yuntsebaryon/SLArchettoHeaterControl/Schematic/GasHeaterControl/GasHeaterControl.kicad_sch

## KiCad design Schematic/GasHeaterControl/GasHeaterControl.kicad_sch (2023-05-16)

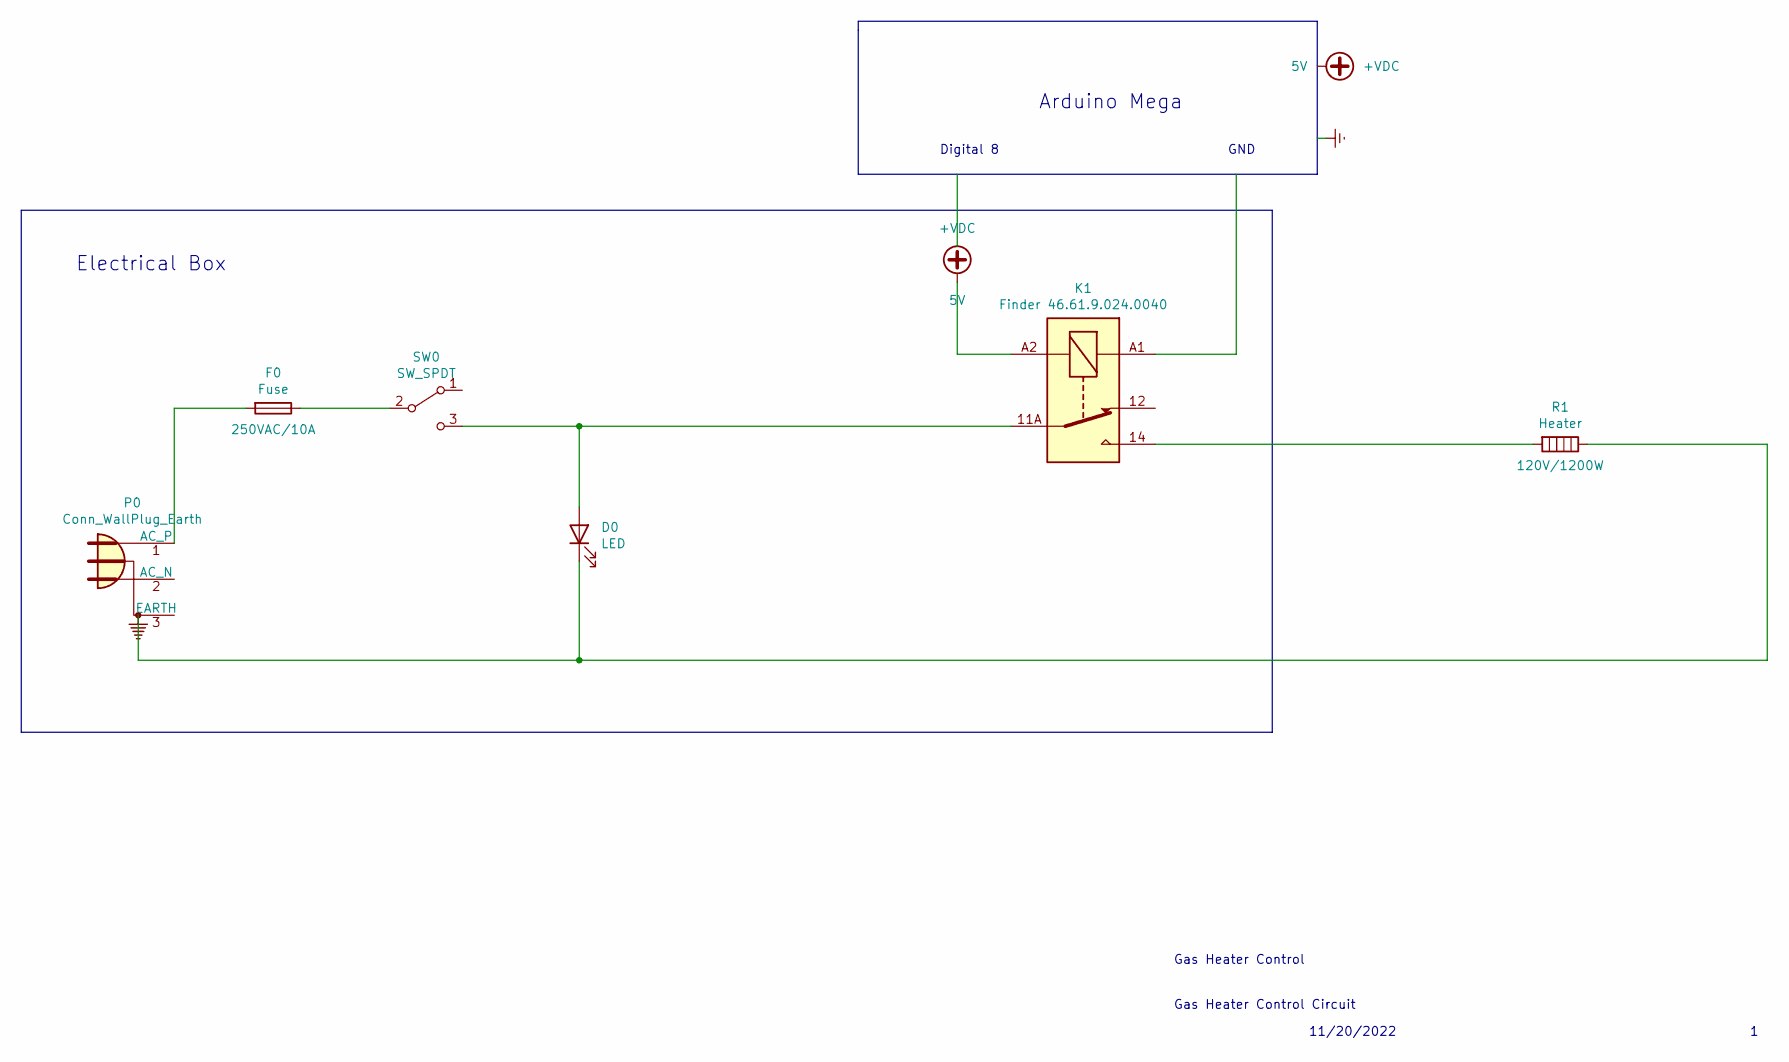
[picture p6: schematic GasHeaterControl.kicad_sch]

Parts:
5V: +VDC
D0: LED
F0: Fuse
K1: Finder 46.61.9.024.0040; Relay_SPDT_RAYEX-L90
P0: Conn_WallPlug_Earth
R1: Heater
SW0: SW_SPDT

Connections:
unnamed: 5V.1, K1.A2
unnamed: D0.1 (K), R1.1
unnamed: D0.2 (A), K1.11A, K1.11B, SW0.3 (C)
unnamed: F0.1, SW0.2 (B)
unnamed: F0.2, P0.1 (AC_P)
unnamed: K1.14, R1.2

Notes on the sheet:
Gas Heater Control Circuit
Digital 8
Arduino Mega
GND
Electrical Box
11/20/2022
Gas Heater Control
