yuntsebaryon/SLArchettoHeaterControl/Schematic/LArHeaterControl/LArHeaterControl.kicad_sch

## KiCad design Schematic/LArHeaterControl/LArHeaterControl.kicad_sch (2022-11-20)

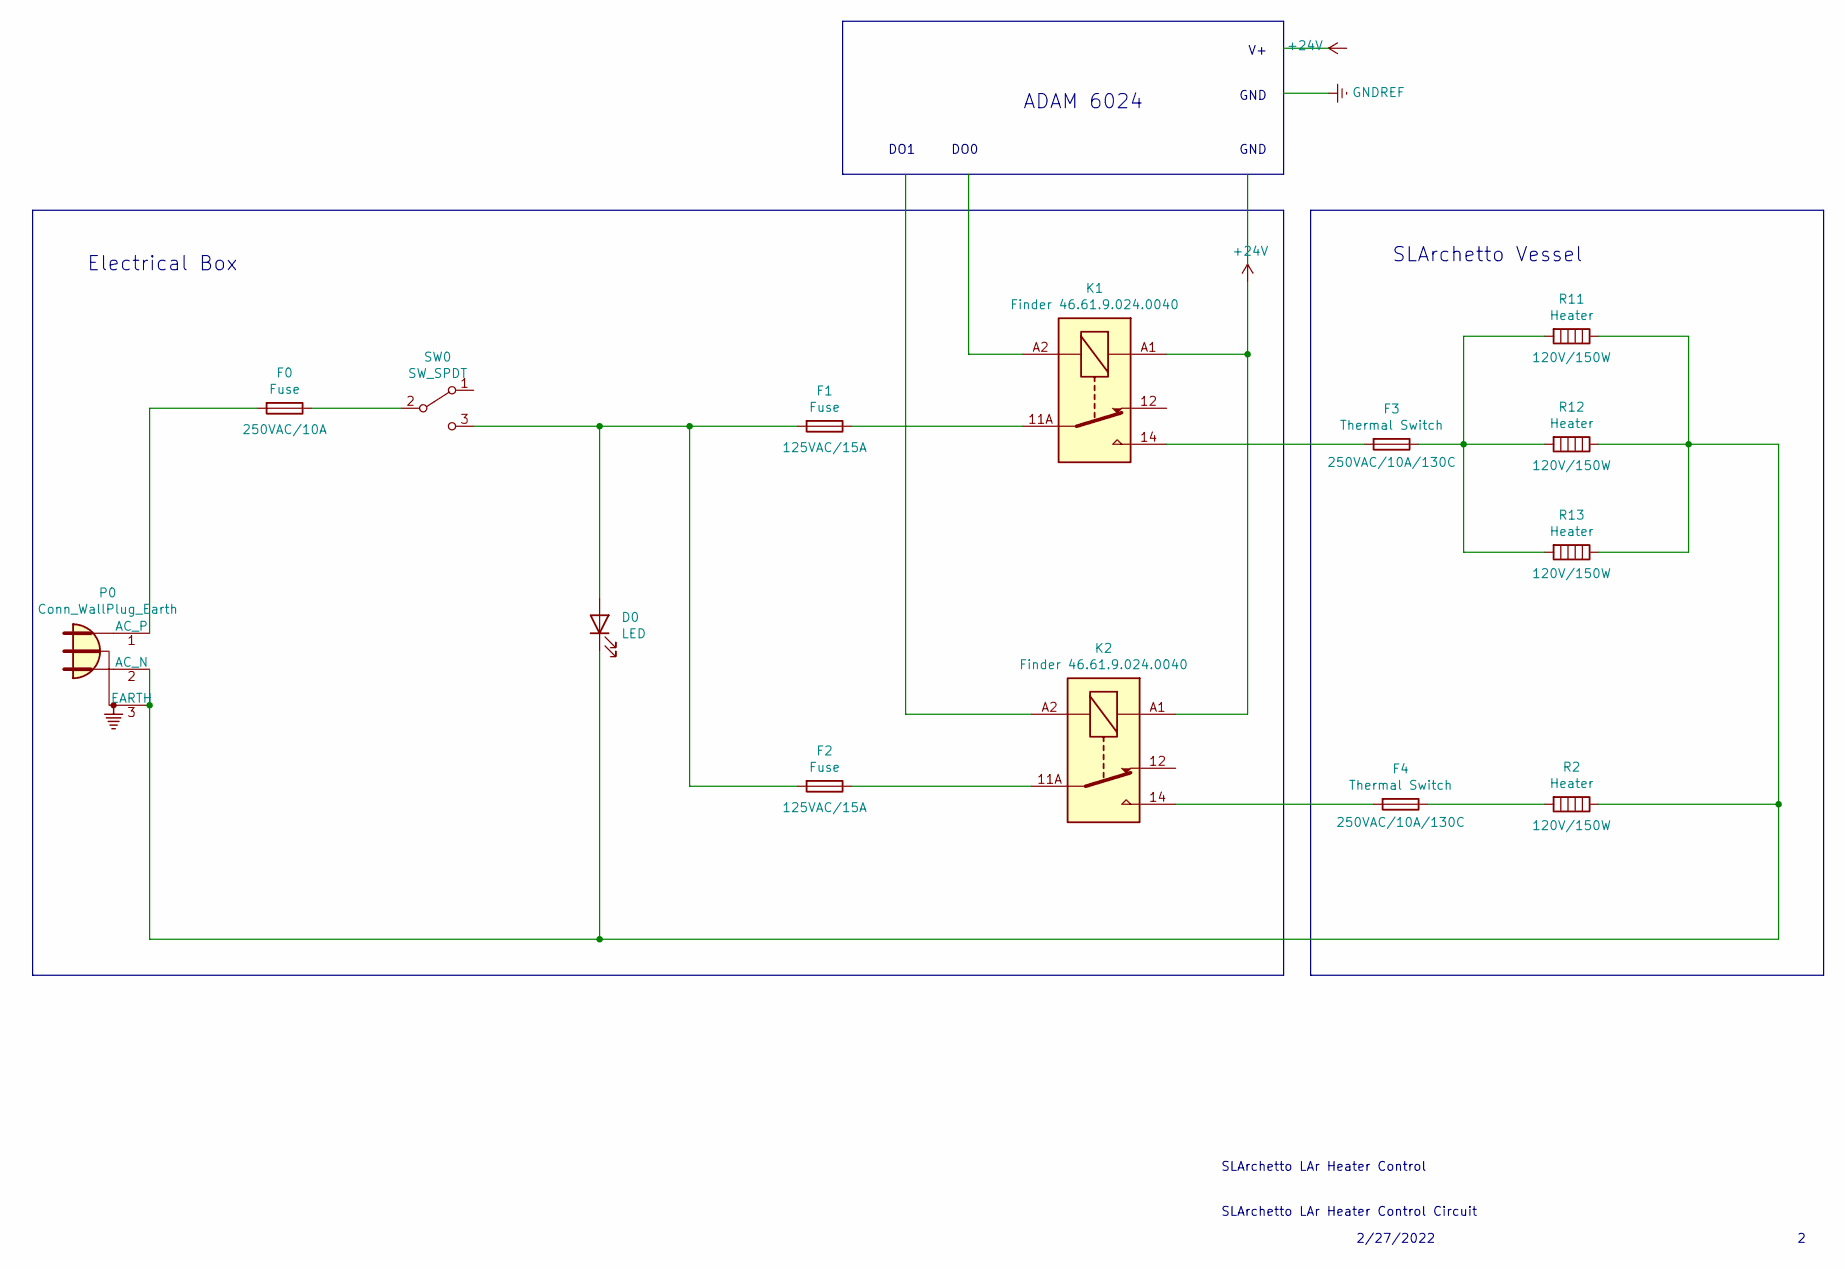
[picture p7: schematic LArHeaterControl.kicad_sch]

Parts:
D0: LED
F0, F1, F2: Fuse
F3, F4: Thermal Switch
K1, K2: Finder 46.61.9.024.0040; Relay_SPDT_RAYEX-L90
P0: Conn_WallPlug_Earth
R2, R11, R12, R13: Heater
SW0: SW_SPDT

Connections:
unnamed: D0.1 (K), P0.2 (AC_N), P0.3 (EARTH), R2.1, R11.1, R12.1, R13.1
unnamed: D0.2 (A), F1.2, F2.2, SW0.3 (C)
unnamed: F0.1, SW0.2 (B)
unnamed: F0.2, P0.1 (AC_P)
unnamed: F1.1, K1.11A, K1.11B
unnamed: F2.1, K2.11A, K2.11B
unnamed: F3.1, R11.2, R12.2, R13.2
unnamed: F3.2, K1.14
unnamed: F4.1, R2.2
unnamed: F4.2, K2.14
unnamed: K1.A1, K2.A1

Notes on the sheet:
ADAM 6024
SLArchetto Vessel
DO1
GND
SLArchetto LAr Heater Control Circuit
2/27/2022
DO0
Electrical Box
SLArchetto LAr Heater Control
